AshishA26/OmniBot/Models/OmniBotAssembly/Arduino Mega 2560.SLDPRT

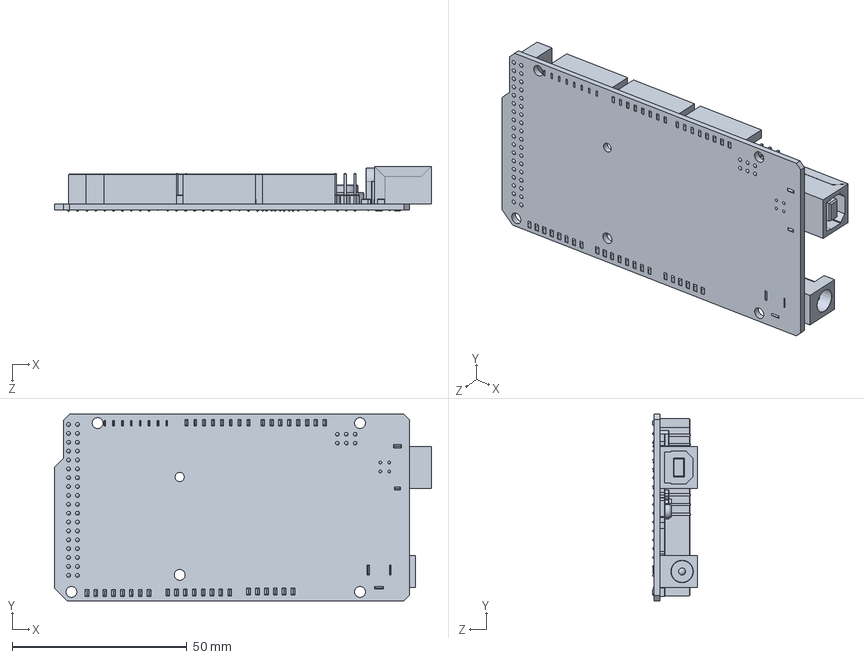
[picture p25: CAD file, 2021-12-24]
Models/OmniBotAssembly/Arduino Mega 2560.SLDPRT
107.9 x 53.4 x 13.0 mm
