AshishA26/OmniBot/Models/OmniBotAssembly/Motor.SLDPRT

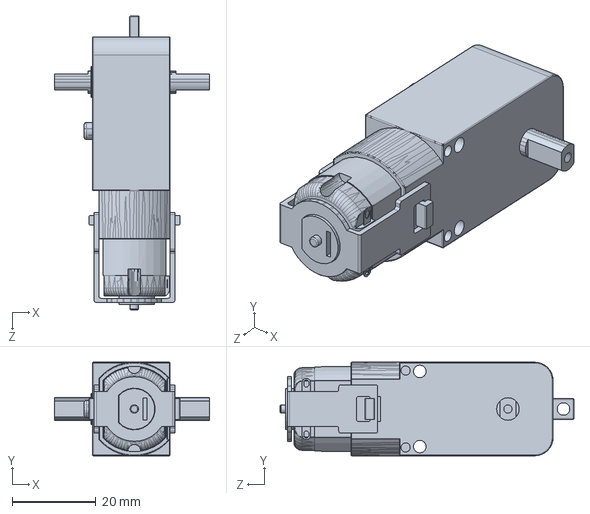
[picture p26: CAD file, 2021-12-24]
Models/OmniBotAssembly/Motor.SLDPRT
37.1 x 22.4 x 70.3 mm
