AshishA26/OmniBot/Models/OmniBotAssembly/encoder20p.SLDPRT

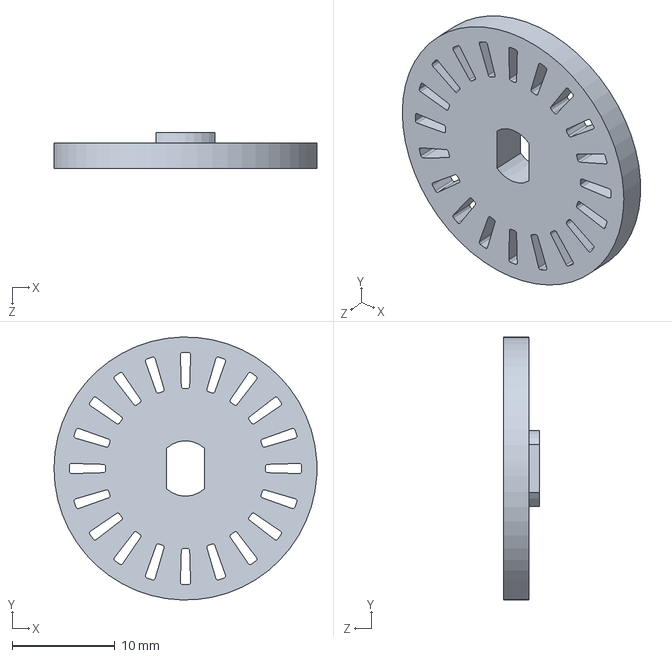
[picture p27: CAD file, 2021-12-24]
Models/OmniBotAssembly/encoder20p.SLDPRT
25.6 x 25.6 x 3.50 mm
