AshishA26/OmniBot/Models/OmniBotAssembly/AA Duracell Body.SLDPRT

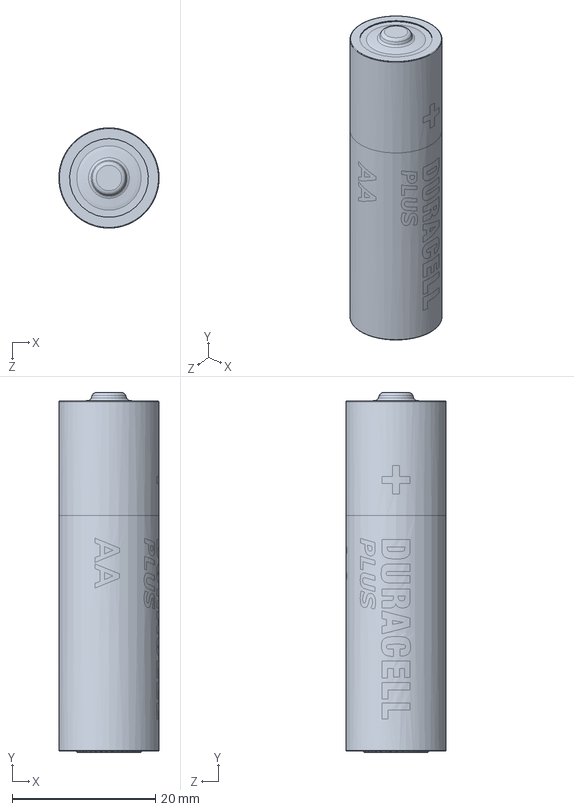
[picture p28: CAD file, 2021-12-24]
Models/OmniBotAssembly/AA Duracell Body.SLDPRT
14.0 x 50.2 x 14.0 mm
