AshishA26/OmniBot/Models/OmniBotAssembly/Lm393 Motor Speed Measuring Sensor Module.SLDPRT

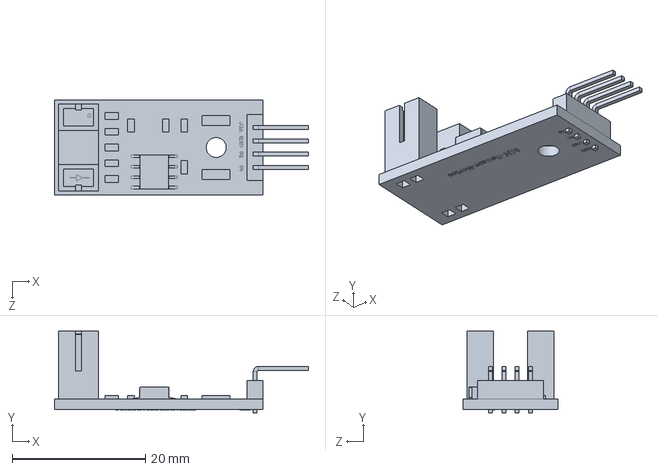
[picture p29: CAD file, 2021-12-24]
Models/OmniBotAssembly/Lm393 Motor Speed Measuring Sensor Module.SLDPRT
38.1 x 12.3 x 14.2 mm
