AshishA26/OmniBot/Models/OmniBotAssembly/Motor Stand.SLDPRT

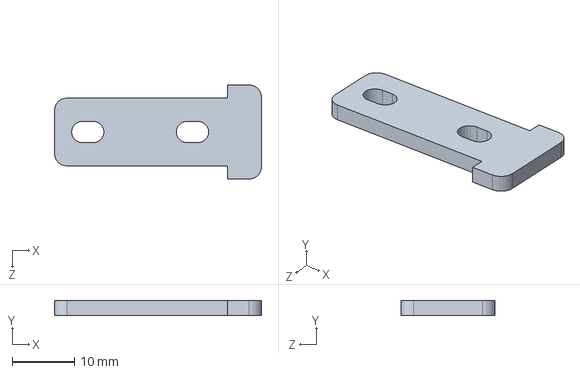
[picture p30: CAD file, 2021-12-24]
Models/OmniBotAssembly/Motor Stand.SLDPRT
33.3 x 2.40 x 15.2 mm
