AshishA26/OmniBot/Images/OmniBot-Schematic-UsingTags/OmniBot-Schematic.kicad_pcb

## KiCad design doc/schematics/espboard/espboard.sch

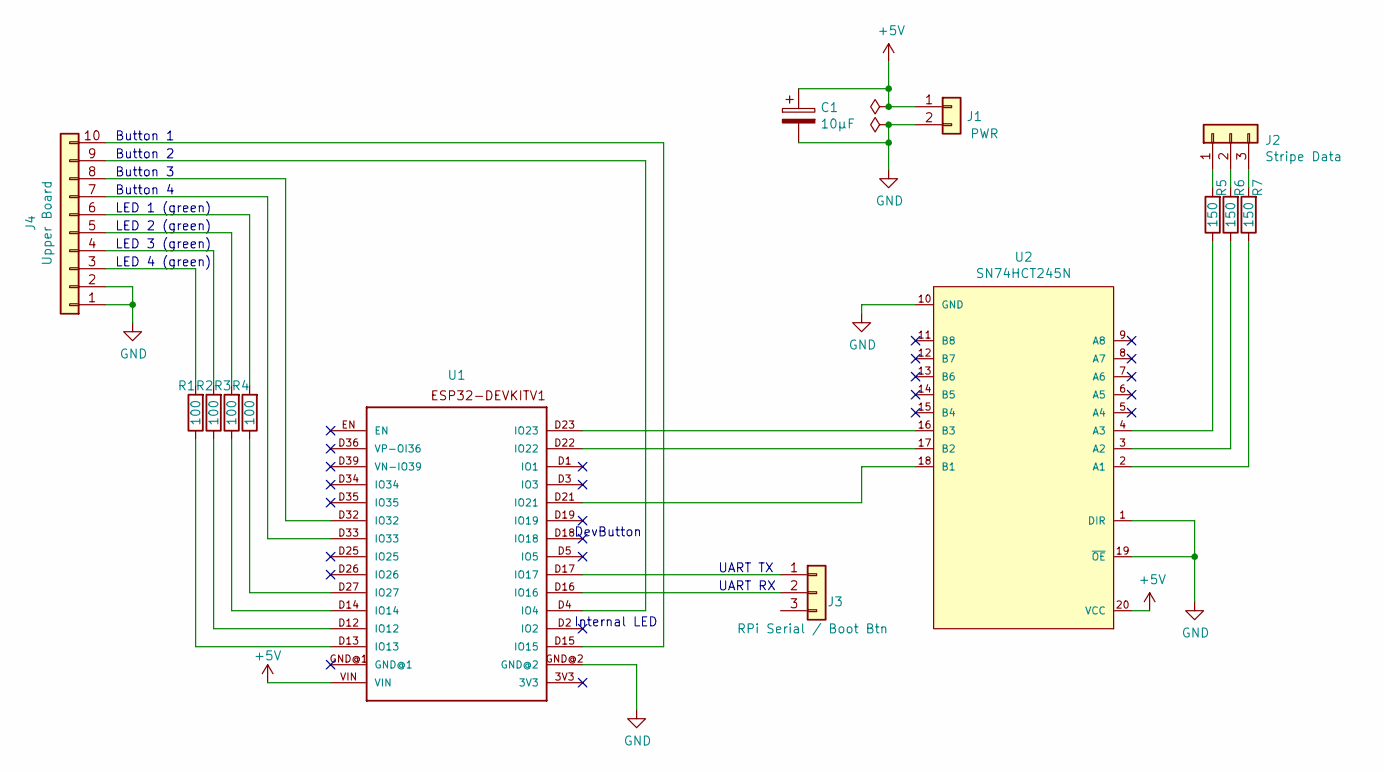
[picture p35: schematic espboard.sch]

Parts:
C1: 10µF
J1: PWR
J2: Stripe Data
J3: RPi Serial / Boot Btn
J4: Upper Board
R1, R2, R3, R4: 100
R5, R6, R7: 150
U1: ESP32DEVKITV1; ESP32-DEVKITV1
U2: SN74HCT245N; Texas_Instruments-SN74HCT245N-0-0-MFG; mouser part number 595-SN74HCT245N; digikey description IC TXRX NON-INVERT 5.5V 20DIP

Connections:
+5V: C1.1, J1.1, U1.VIN, U2.20 (VCC)
GND: C1.2, J1.2, J4.1, J4.2, U1.GND@2, U2.1 (DIR), U2.10 (GND), U2.19 (~OE~)
unnamed: J2.1, R5.2
unnamed: J2.2, R6.2
unnamed: J2.3, R7.2
unnamed: J3.1, U1.D17 (IO17)
unnamed: J3.2, U1.D16 (IO16)
unnamed: J4.3, R1.2
unnamed: J4.4, R2.2
unnamed: J4.5, R3.2
unnamed: J4.6, R4.2
unnamed: J4.7, U1.D33 (IO33)
unnamed: J4.8, U1.D32 (IO32)
unnamed: J4.9, U1.D4 (IO4)
unnamed: J4.10, U1.D15 (IO15)
unnamed: R1.1, U1.D13 (IO13)
unnamed: R2.1, U1.D12 (IO12)
unnamed: R3.1, U1.D14 (IO14)
unnamed: R4.1, U1.D27 (IO27)
unnamed: R5.1, U2.4 (A3)
unnamed: R6.1, U2.3 (A2)
unnamed: R7.1, U2.2 (A1)
unnamed: U1.D21 (IO21), U2.18 (B1)
unnamed: U1.D22 (IO22), U2.17 (B2)
unnamed: U1.D23 (IO23), U2.16 (B3)

Notes on the sheet:
UART TX
UART RX
LED 1 (green)
Button 2
Button 3
Button 4
LED 2 (green)
Internal LED
LED 3 (green)
LED 4 (green)
DevButton
Button 1
